Burgestrand/V1.324/software/voron.local/printer/probe/z_probe.cfg

[probe]
pin: ^EBBCan: ESTOP1
x_offset: 0
y_offset: 19.75
z_offset: 6.42 # Z7.2 on probe, Z0.2 on nozzle
speed: 5
samples: 3
samples_result: median
sample_retract_dist: 2.0
samples_tolerance: 0.01
samples_tolerance_retries: 5
