Burgestrand/V1.324/software/voron.local/printer/bed.cfg

[heater_bed]
heater_pin: HE0
min_temp: 10
max_temp: 118

# Heater: Keenovo 200x200, 400W
# Maximum power 0.4W/cm2
#
# Full Bed: 250x250 = 625cm2 * 0.4W = 250W
# 250W (max) / 400W (bed) = 0.625
#
# Full Heater: 200x200 = 400cm2 * 0.4W = 160W
# 160W (max) / 400W (bed) = 0.4
max_power: 0.625

# Thermistor
sensor_pin: TB
sensor_type: Generic 3950

# Use Z_TILT_ADJUST to level the bed left to right.
[z_tilt]
# z_tilt positions matches the positions of the bearing centers
# (the pivot points) to the CAD.
z_positions:
  299, 17
  121, 302
  -46, 17
# points on the bed to probe for each z_position
points:
  6, 9
  245, 9
  121, 209
speed: 200
horizontal_move_z: 15
retries: 5
retry_tolerance: 0.0075

[bed_mesh]
speed: 300
horizontal_move_z: 10
# probe offset: (1,19.75)
mesh_min: 5,25 # = X0 Y-0.75
mesh_max: 240, 240 # X244 Y225.25
fade_start: 1
fade_end: 10.0
probe_count: 5,5
algorithm: bicubic
zero_reference_position: 122.5, 132.5
adaptive_margin: 10
