Burgestrand/V1.324/software/voron.local/printer/tune/e_steps.cfg

[extruder]
min_temp: -100
min_extrude_temp: -100
