Burgestrand/V1.324/software/voron.local/printer/macros/start-stop.cfg

[gcode_macro PRINT_START]
gcode:
  {% set bed_temp = params.BED|float %}
  {% set extruder_temp = params.EXTRUDER|float %}
  {% set extruder_prime = 150 %}
  {% set nozzle_diameter = params.NOZZLE_DIAMETER|float %}
  {% set klipper_nozzle_diameter = printer.configfile.settings.extruder.nozzle_diameter %}

  {% if nozzle_diameter != klipper_nozzle_diameter %}
    { action_raise_error("Slicer nozzle was " ~ nozzle_diameter ~ " but Klipper is " ~ klipper_nozzle_diameter) }
    status_off
  {% endif %}

  status_ready

  ; {% if params.FILAMENT == "ABS" %} - why not always?
  NEVERMORE_ON
  ; {% endif %}

  ; Make sure we start heating up right away
  M104 S{extruder_prime}
  M140 S{bed_temp}

  status_homing
  M117 Homing all axes!
  MAYBE_HOME

  status_heating
  M117 Heating bed!
  M190 S{bed_temp} ; set bed temp and wait

  M117 Heating extruder!
  M109 S{extruder_prime} ; safe temp to avoid ooze

  M117 Calibrating!
  CALIBRATE EXTRUDER={extruder_temp}

  # M117 Heating and purging!
  # PURGE_BUCKET EXTRUDER={extruder_temp}

  status_cleaning
  M117 Time to purge!
  PURGE_LINE EXTRUDER={extruder_temp}

  status_printing
  M117 Printing!
  M117

[gcode_macro PRINT_END]
gcode:
  #   Get Boundaries
  {% set max_x = printer.configfile.config["stepper_x"]["position_max"]|float %}
  {% set max_y = printer.configfile.config["stepper_y"]["position_max"]|float %}
  {% set max_z = printer.configfile.config["stepper_z"]["position_max"]|float %}
  {% set x_offset = 20 %}
  {% set y_offset = 20 %}
  {% set z_offset = 20 %}
  {% set park_x = 170 %}
  {% set park_y = max_y %}
  
  #   Check end position to determine safe directions to move
  {% if printer.toolhead.position.x < (max_x - x_offset) %}
      {% set x_safe = x_offset %}
  {% else %}
      {% set x_safe = -x_offset %}
  {% endif %}

  {% if printer.toolhead.position.y < (max_y - y_offset) %}
      {% set y_safe = y_offset %}
  {% else %}
      {% set y_safe = -y_offset %}
  {% endif %}

  {% if printer.toolhead.position.z < (max_z - z_offset) %}
      {% set z_safe = z_offset %}
  {% else %}
      {% set z_safe = max_z - printer.toolhead.position.z %}
  {% endif %}
  
  #  Commence PRINT_END
  M400                             ; wait for buffer to clear
  G92 E0                           ; zero the extruder
  G1 E-4.0 F3600                   ; retract
  G91                              ; relative positioning
  G0 Z{z_safe} F3600               ; move nozzle up
  G0 X{x_safe} Y{y_safe} F20000    ; move nozzle to remove stringing

  ; Remove filament
  UNLOAD_EXTRUDER

  ; Exhaust for 5 minutes
  UPDATE_DELAYED_GCODE ID=NEVERMORE_TIMEOUT DURATION=600
  
  M104 S0                          ; turn off hotend
  M140 S0                          ; turn off bed
  M106 S0                          ; turn off fan
  G90                              ; absolute positioning
  G0 X{park_x} Y{park_y} F3600     ; park nozzle
  M117 Finished!
