Burgestrand/V1.324/software/voron.local/printer/input_shaper/adxl345.cfg

[mcu rpi]
serial: /tmp/klipper_host_mcu

[adxl345]
cs_pin: rpi:None

[resonance_tester]
accel_chip: adxl345
probe_points:
  125,125,50  # an example
